TomConlin/Sudiball/sixF8/classic_6in_tube_sudibal_sagl.dxf

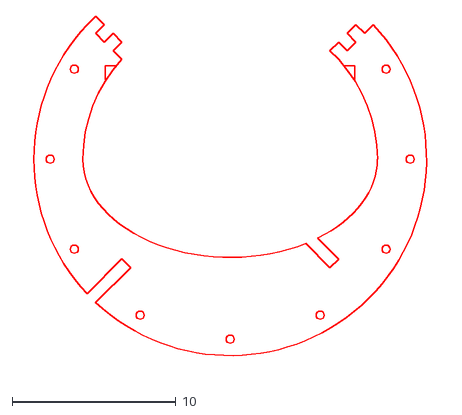
[picture p21: CAD file, 2017-06-25]
sixF8/classic_6in_tube_sudibal_sagl.dxf
26.3 x 21.9
