TomConlin/Sudiball/TenF4_5/laz1.1.dxf

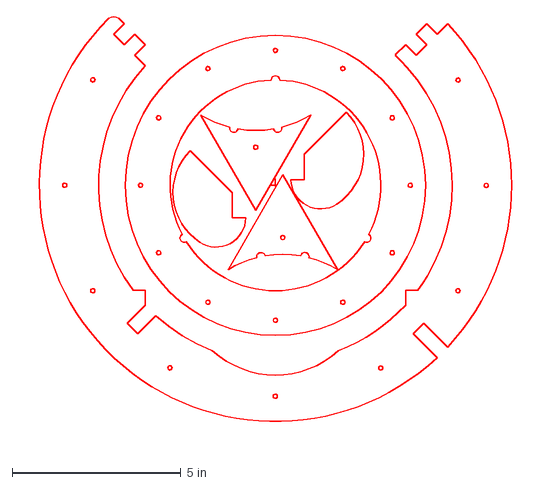
[picture p22: CAD file, 2020-03-29]
TenF4_5/laz1.1.dxf
15.3 x 12.7 in
