TomConlin/Sudiball/TenF4_5/sudigen.dxf

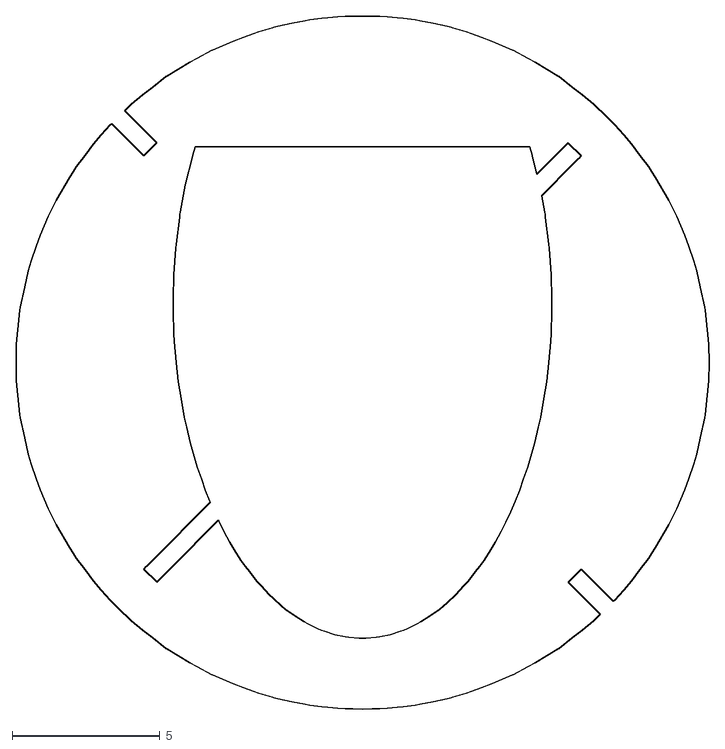
[picture p23: CAD file, 2020-03-29]
TenF4_5/sudigen.dxf
23.5 x 23.5
