TomConlin/Sudiball/Travel_8-F4/layout2.1.dxf

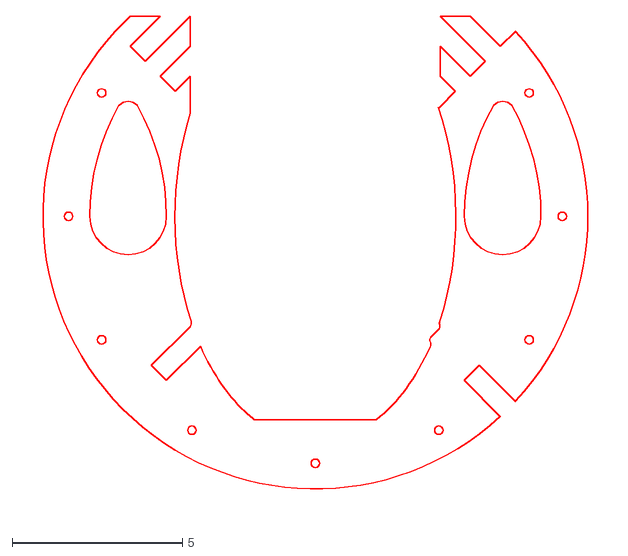
[picture p24: CAD file, 2020-03-29]
Travel_8-F4/layout2.1.dxf
17.5 x 14.7
