TomConlin/Sudiball/sixF8/sudigen.dxf

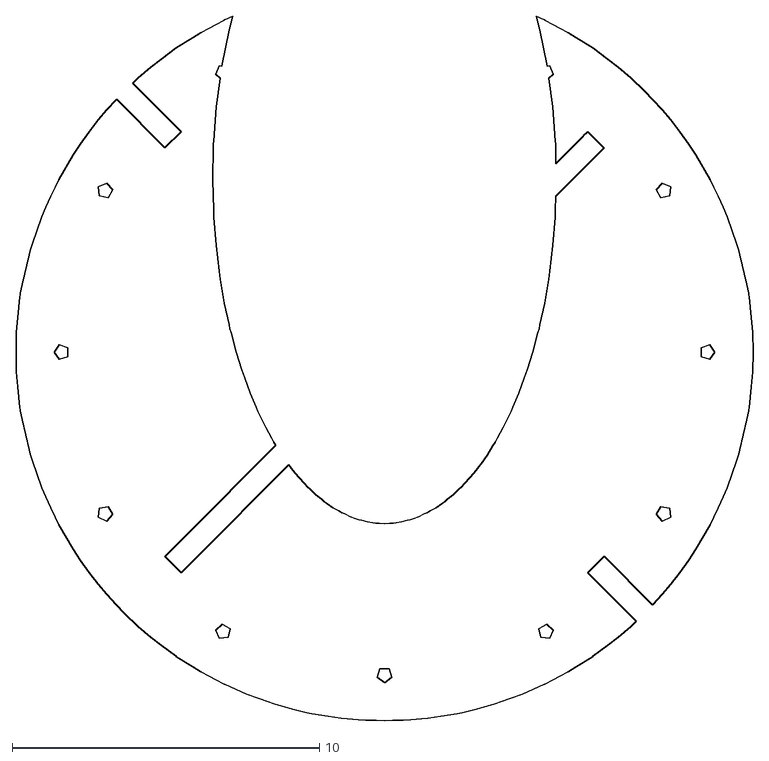
[picture p25: CAD file, 2017-03-28]
sixF8/sudigen.dxf
24.0 x 22.9
