TomConlin/Sudiball/Travel_8-F4/layout2_plns_cam.dxf

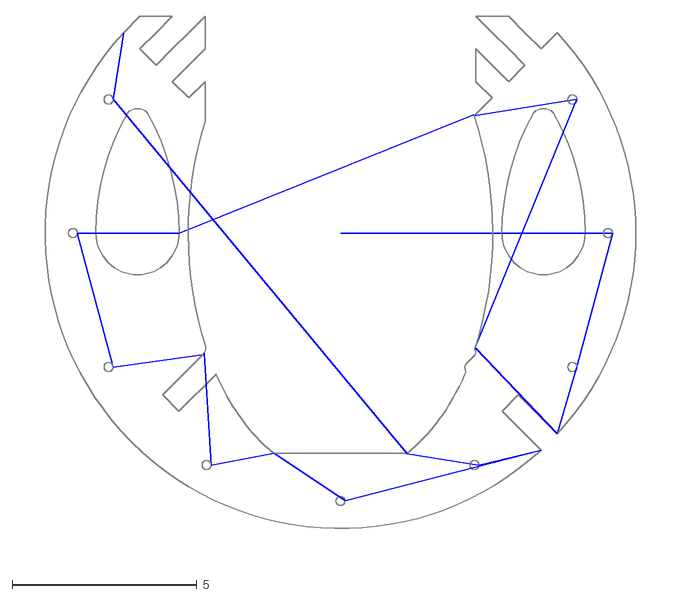
[picture p26: CAD file, 2020-03-29]
Travel_8-F4/layout2_plns_cam.dxf
17.5 x 14.7
