TomConlin/Sudiball/Travel_8-F4/layout3.2_sag.dxf

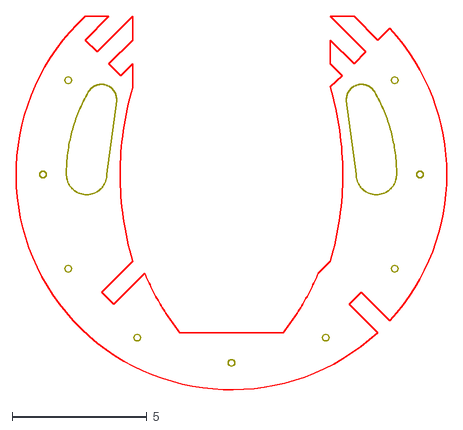
[picture p28: CAD file, 2020-03-29]
Travel_8-F4/layout3.2_sag.dxf
16.0 x 13.9
