TomConlin/Sudiball/Travel_8-F4/layout3.3.dxf

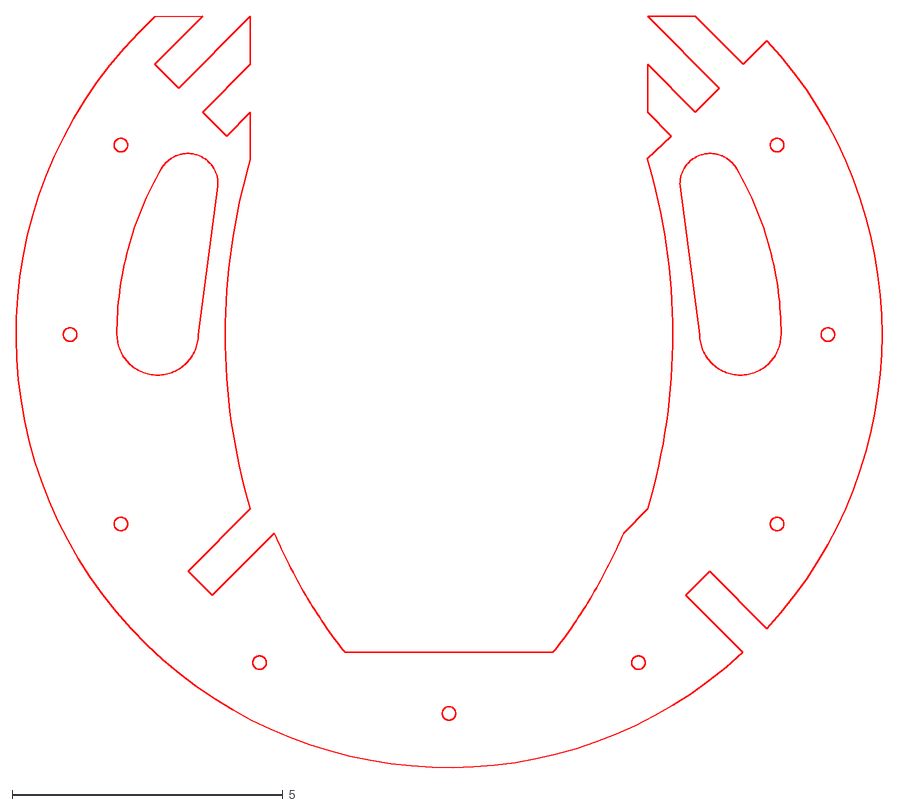
[picture p29: CAD file, 2020-03-29]
Travel_8-F4/layout3.3.dxf
16.0 x 13.9
