TomConlin/Sudiball/Travel_8-F4/layout3.2_outline.dxf

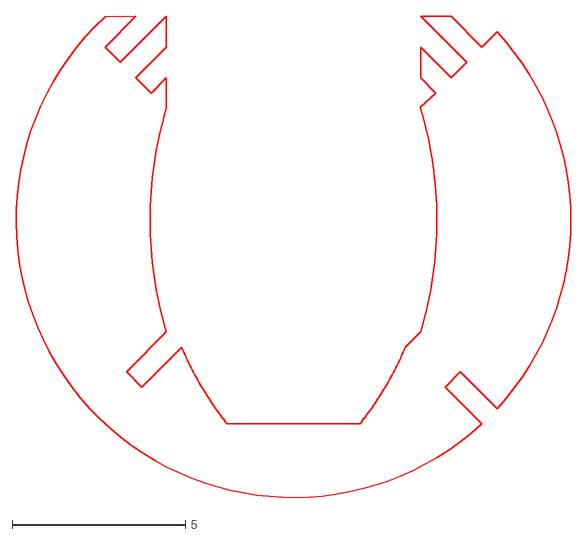
[picture p30: CAD file, 2020-03-29]
Travel_8-F4/layout3.2_outline.dxf
16.0 x 13.9
