TomConlin/Sudiball/Travel_8-F4/layout3.2_extrude.dxf

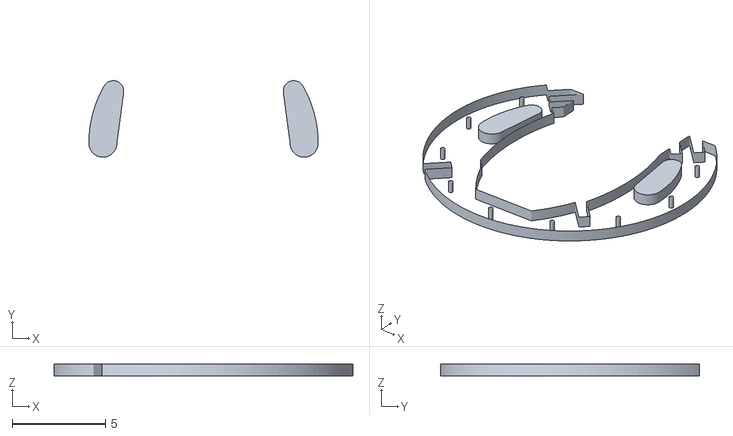
[picture p32: CAD file, 2020-03-29]
Travel_8-F4/layout3.2_extrude.dxf
16.0 x 13.9 x 0.625
