TomConlin/Sudiball/Travel_8-F4/sudigen_3.4.dxf

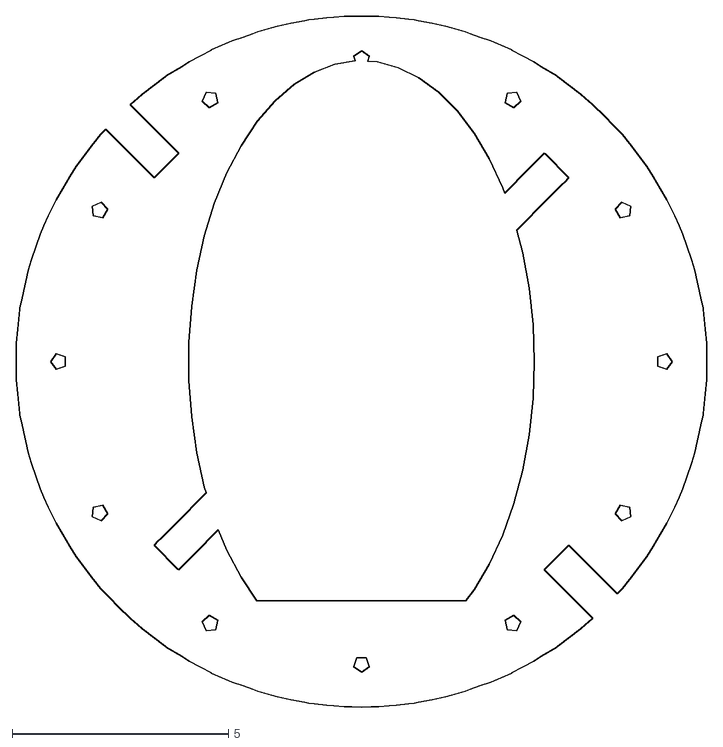
[picture p33: CAD file, 2020-03-29]
Travel_8-F4/sudigen_3.4.dxf
16.0 x 16.0
