TomConlin/Sudiball/Travel_8-F4/layout3.2.dxf

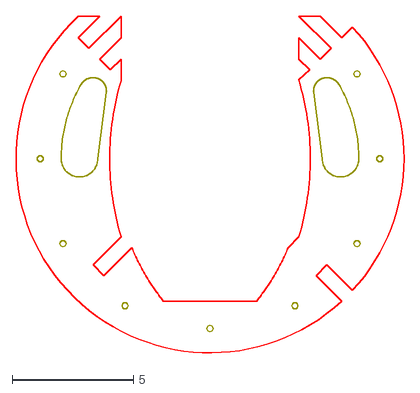
[picture p34: CAD file, 2020-03-29]
Travel_8-F4/layout3.2.dxf
16.0 x 13.9
