TomConlin/Sudiball/Travel_8-F4/layout2.2_flip.dxf

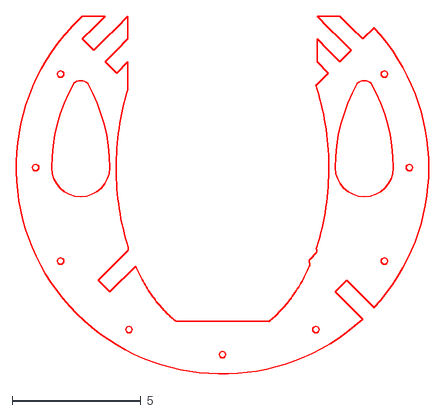
[picture p35: CAD file, 2020-03-29]
Travel_8-F4/layout2.2_flip.dxf
16.0 x 13.9
