TomConlin/Sudiball/Travel_8-F4/sudigen.dxf

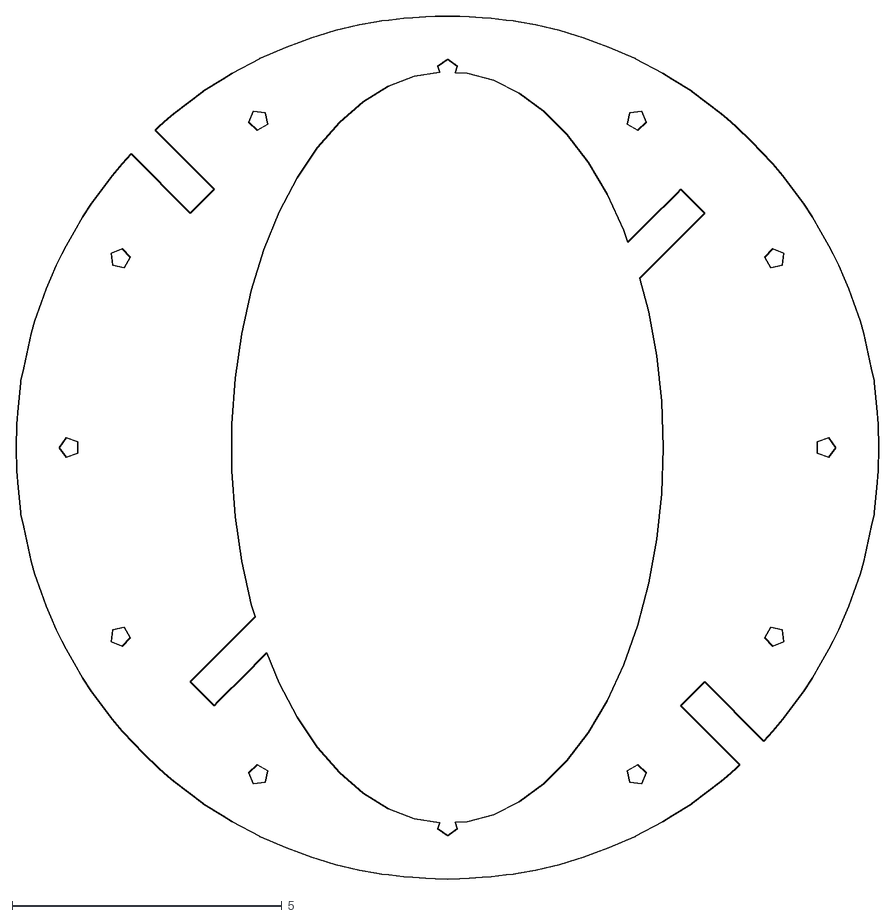
[picture p36: CAD file, 2020-03-29]
Travel_8-F4/sudigen.dxf
16.0 x 16.0
