TomConlin/Sudiball/Travel_8-F4/layout3.0.dxf

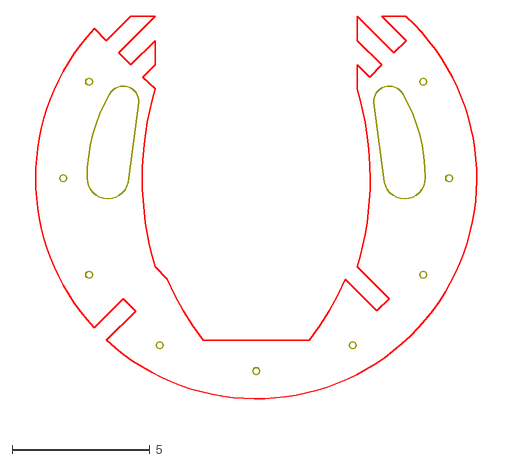
[picture p37: CAD file, 2020-03-29]
Travel_8-F4/layout3.0.dxf
17.6 x 14.8
