TomConlin/Sudiball/Travel_8-F4/layout3.2.1.dxf

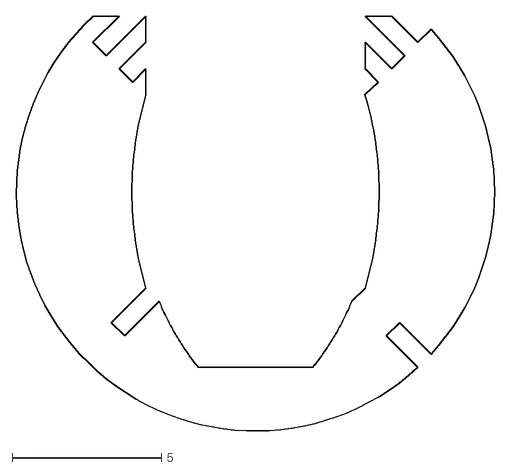
[picture p38: CAD file, 2020-03-29]
Travel_8-F4/layout3.2.1.dxf
16.0 x 13.9
