TomConlin/Sudiball/Travel_8-F4/layout3.2_extrude_FC.dxf

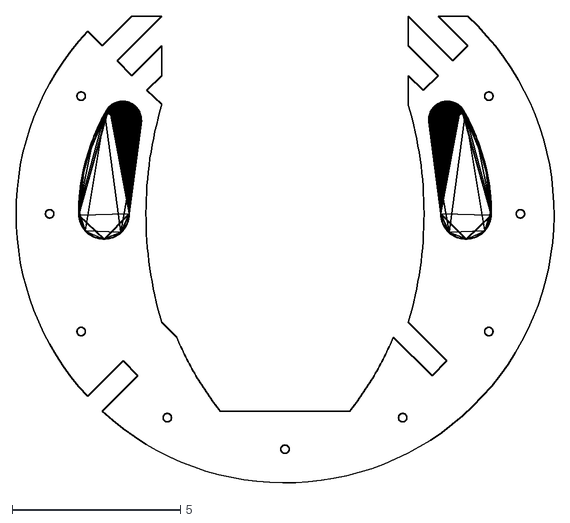
[picture p39: CAD file, 2020-03-29]
Travel_8-F4/layout3.2_extrude_FC.dxf
16.0 x 13.9
