TomConlin/Sudiball/Travel_8-F4/layout2.4.dxf

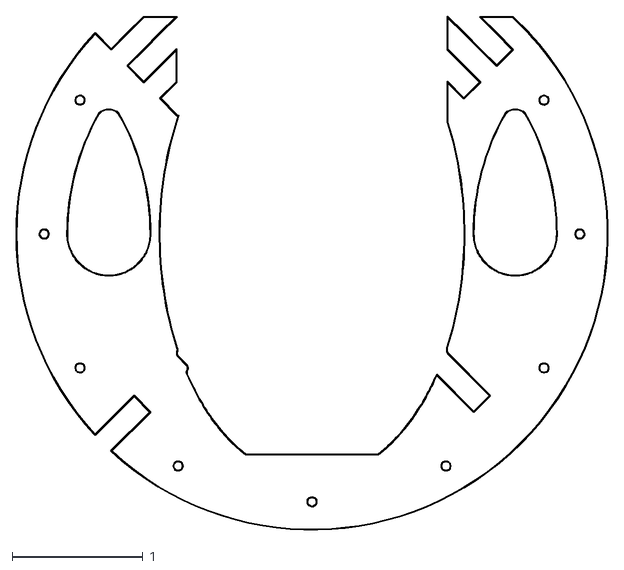
[picture p40: CAD file, 2020-03-29]
Travel_8-F4/layout2.4.dxf
4.52 x 3.92
