TomConlin/Sudiball/TenF4_5/freecad_dxf_to_oscad.scad

// CSG file generated from FreeCAD 0.15.4671 (Git)
group() {
 group(){
