TomConlin/Sudiball/Travel_8-F4/dxf_import.scad

import("/home/tomc/GitHub/Sudiball/Travel_8-F4/layout3.2.1.dxf", convexity = 10);
